hemrobotics/reprap-printer/parts/prusa-i3-mod/y-belt-holder.FCStd

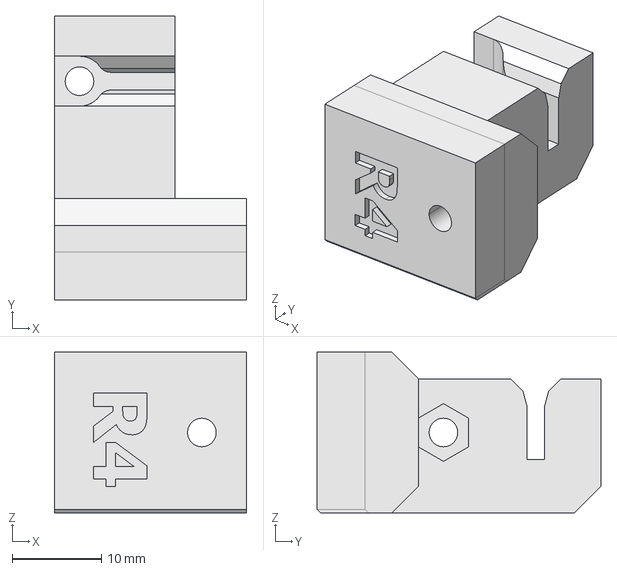
[picture p17: CAD file, 2022-03-06]
parts/prusa-i3-mod/y-belt-holder.FCStd
21.5 x 31.8 x 18.0 mm
