hemrobotics/reprap-printer/parts/tnut-m8-holder/tnut-m8-holder-bottom.stl

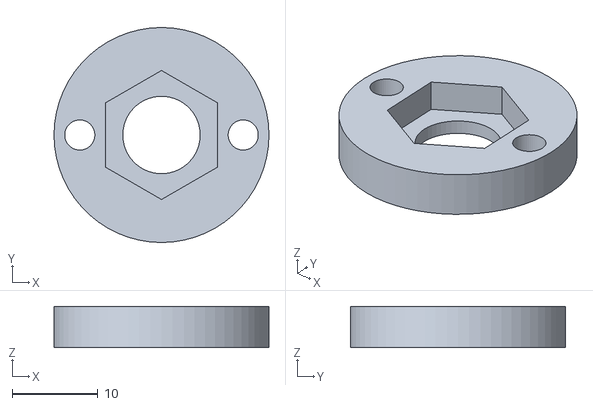
[picture p18: CAD file, 2022-03-06]
parts/tnut-m8-holder/tnut-m8-holder-bottom.stl
25.0 x 25.0 x 4.80
