hemrobotics/reprap-printer/parts/x-carriage-wire-holder/x-carriage-wire-holder-ring.FCStd

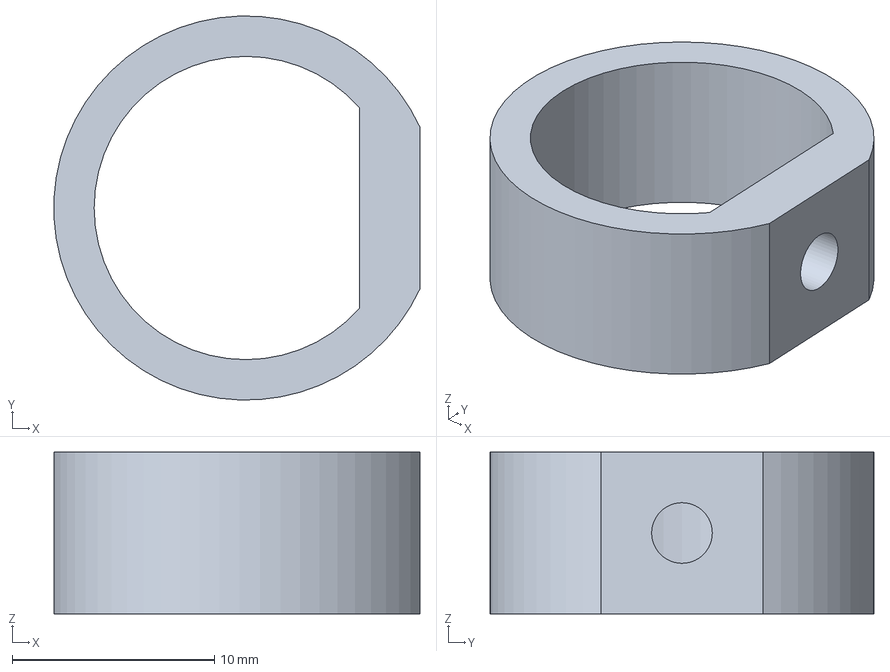
[picture p19: CAD file, 2022-03-06]
parts/x-carriage-wire-holder/x-carriage-wire-holder-ring.FCStd
18.1 x 19.0 x 8.00 mm
