hemrobotics/reprap-printer/parts/y-endstop/y-endstop-plug.FCStd

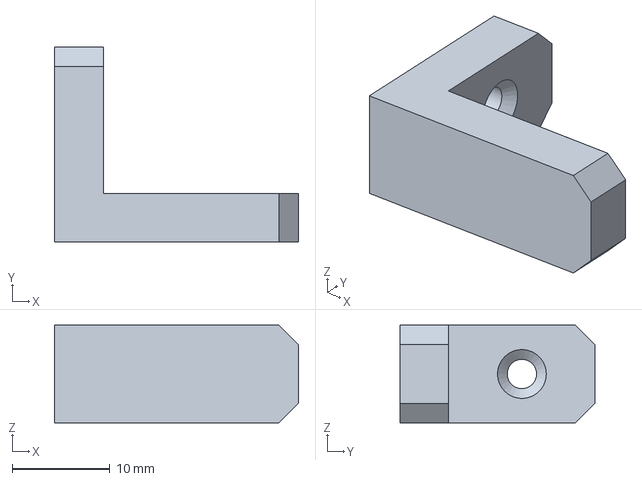
[picture p20: CAD file, 2022-03-06]
parts/y-endstop/y-endstop-plug.FCStd
25.0 x 20.0 x 10.0 mm
