hemrobotics/reprap-printer/parts/z-side-support/z-side-support-bottom.FCStd

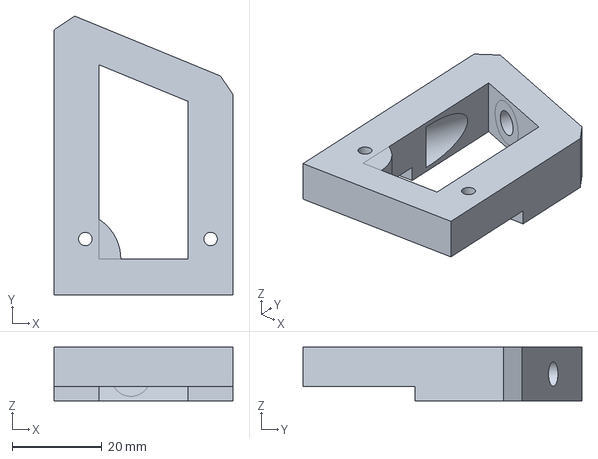
[picture p21: CAD file, 2022-03-06]
parts/z-side-support/z-side-support-bottom.FCStd
40.0 x 62.3 x 12.0 mm
