hemrobotics/reprap-printer/parts/z-support/z-support-bottom.FCStd

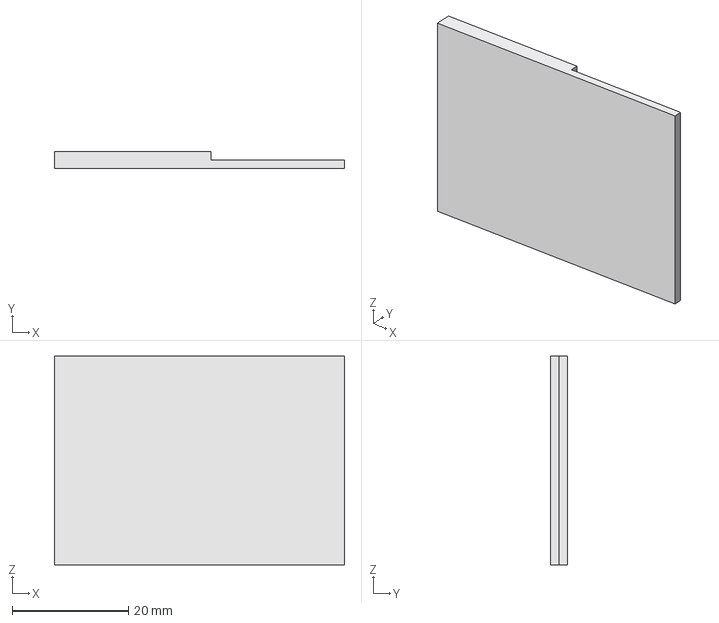
[picture p22: CAD file, 2022-03-06]
parts/z-support/z-support-bottom.FCStd
50.0 x 3.00 x 36.0 mm
