hemrobotics/reprap-printer/parts/arduino-mega-ramps-1.4-box/wire-management-plate.FCStd

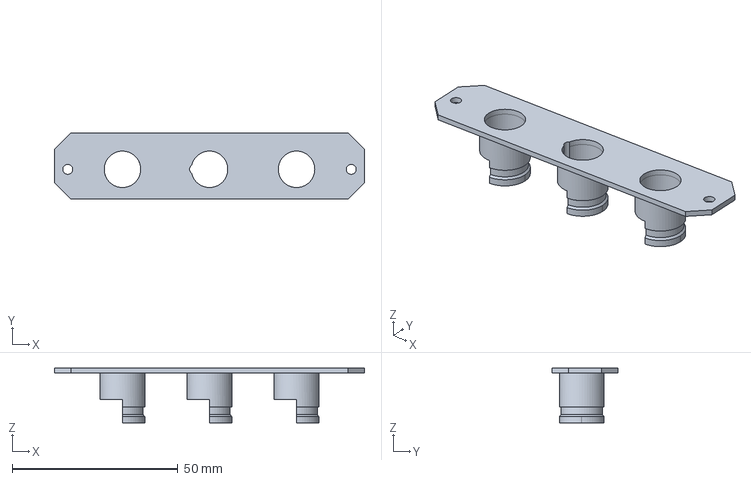
[picture p23: CAD file, 2022-03-06]
parts/arduino-mega-ramps-1.4-box/wire-management-plate.FCStd
93.5 x 20.0 x 16.5 mm
