hemrobotics/reprap-printer/parts/extruder-motor-clamp/extruder-motor-clamp-front.FCStd

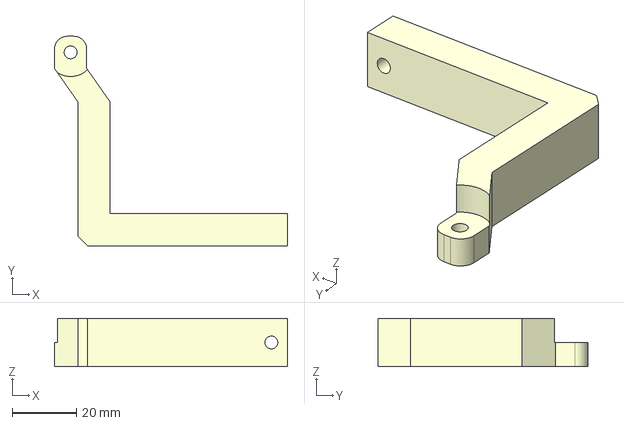
[picture p24: CAD file, 2022-03-06]
parts/extruder-motor-clamp/extruder-motor-clamp-front.FCStd
72.3 x 65.0 x 15.0 mm
