hemrobotics/reprap-printer/parts/prusa-i3-mod/y-belt-tensioner.FCStd

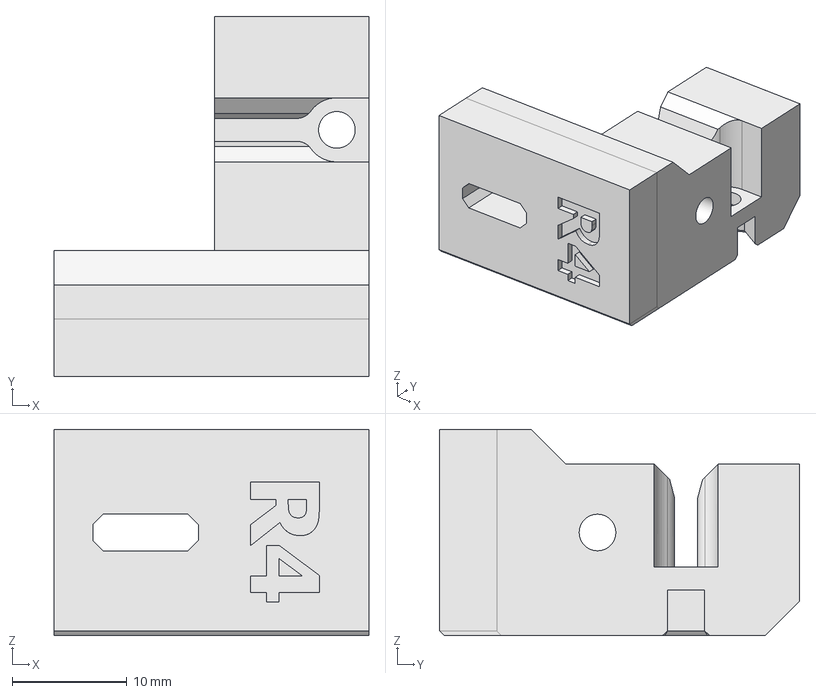
[picture p25: CAD file, 2022-03-06]
parts/prusa-i3-mod/y-belt-tensioner.FCStd
27.5 x 31.4 x 18.0 mm
