hemrobotics/reprap-printer/parts/prusa-i3-mod/y-belt-idler.FCStd

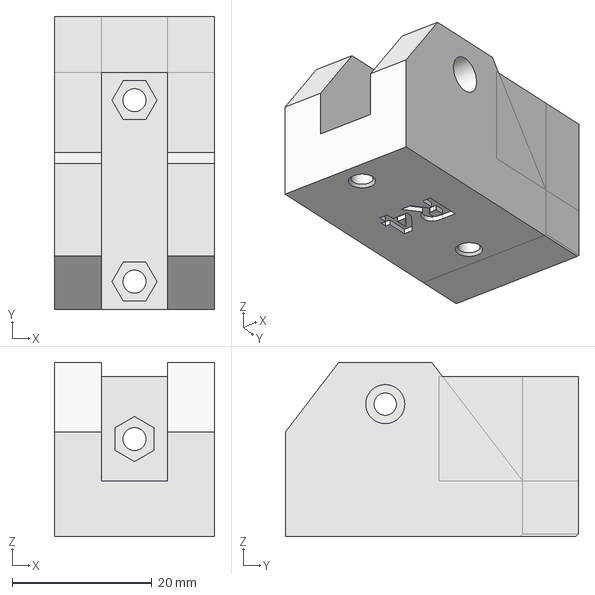
[picture p26: CAD file, 2022-03-06]
parts/prusa-i3-mod/y-belt-idler.FCStd
23.0 x 42.0 x 25.0 mm
