hemrobotics/reprap-printer/parts/prusa-i3-mod/x-end-idler.FCStd

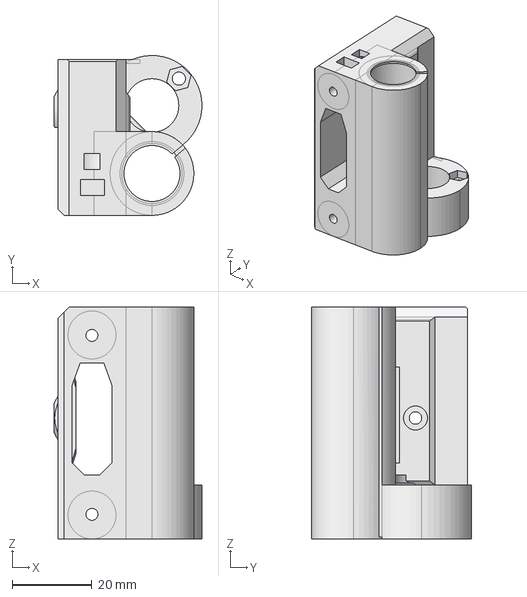
[picture p27: CAD file, 2022-03-06]
parts/prusa-i3-mod/x-end-idler.FCStd
37.0 x 40.0 x 58.0 mm
